PanagiotisPrountzosCS/DistortionPedal/Distortion.asc

C1: cap; 100µ
C2: cap; 0.1µ
C3: cap; 1µ
C4: cap; 1n
C5: cap; 1n
C6: cap; 22n
C7: cap; 4.7µ
C8: cap; 330p
C9: cap; 2.2µ
C10: cap; 4.7µ
C11: cap; 1n
C12: cap; 1µ
C13: cap; 22n
D1: diode; 1N4148
D2: 1N60P
D3: 1N60P
D5: 1N60P; 1N4148
R1: res; 47
R2: res; {Rsup}
R3: res; {Rsup}
R4: res; 47
R5: res; 1Meg
R6: res; 1Meg
R7: res; {Rpottotal - Rpotout + 1}
R8: res; 1k
R9: res; 560
R10: res; {Rpotamp}
R11: res; {Rpotout}
R12: res; 1k
R13: res; {Rtonepot}
R14: res; 1Meg
U1: RC4558
U2: RC4558
V1: voltage; 9
V2: voltage; SINE(0 0.8 10); AC 1
Named nets: 0, VCC, VCC/2, Vamp, Vout
.tran 0 0.5 0
.param Rsup 1Meg
.param Rpotout=100k
.param Rpottotal=100k
.step dec param Rpotamp 1 100k 6
.ac dec 6 1 1Meg
.dc V1 0 12
.param Rtonepot=1k
.lib .\\custom_components\\1N60P.lib
.lib .\\custom_components\\RC4558.301
